drpykachu/Sonar-Watch/Hardware/Complete v3.0/Complete v3.0 3D models/SLDPRT/V3.0.SLDASM

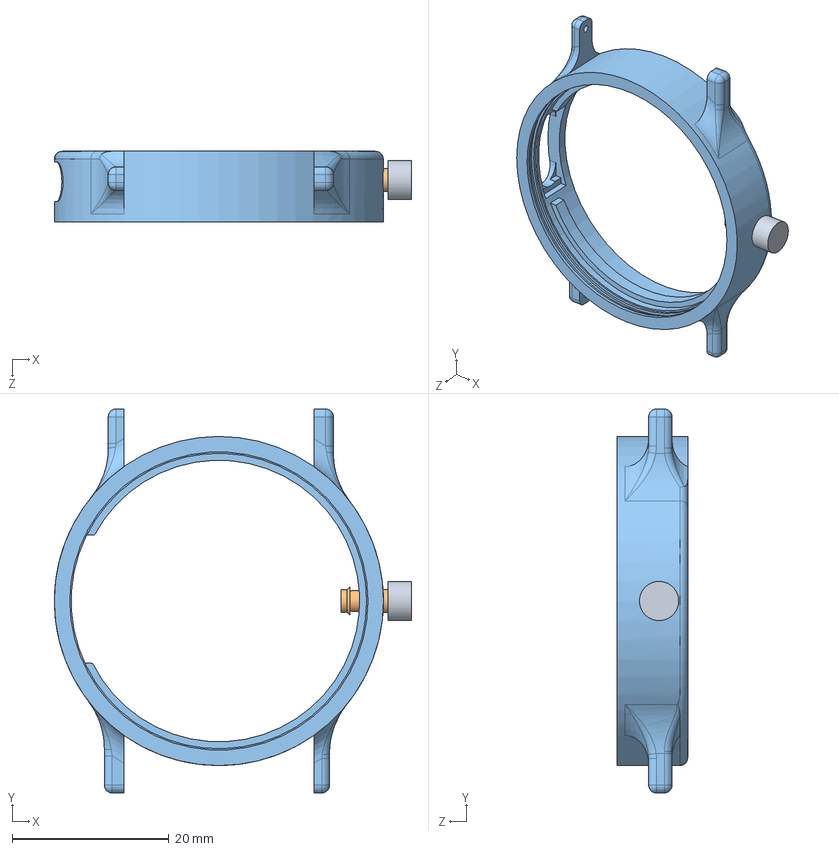
[picture p8: CAD file, 2025-09-28]
Hardware/Complete v3.0/Complete v3.0 3D models/SLDPRT/V3.0.SLDASM
45.6 x 49.0 x 9.00 mm
Body_NoNut
PushPin_inner
PushPin_cap
