drpykachu/Sonar-Watch/Parts/RMCF0603FT300K/RMCF0603FT300K.step

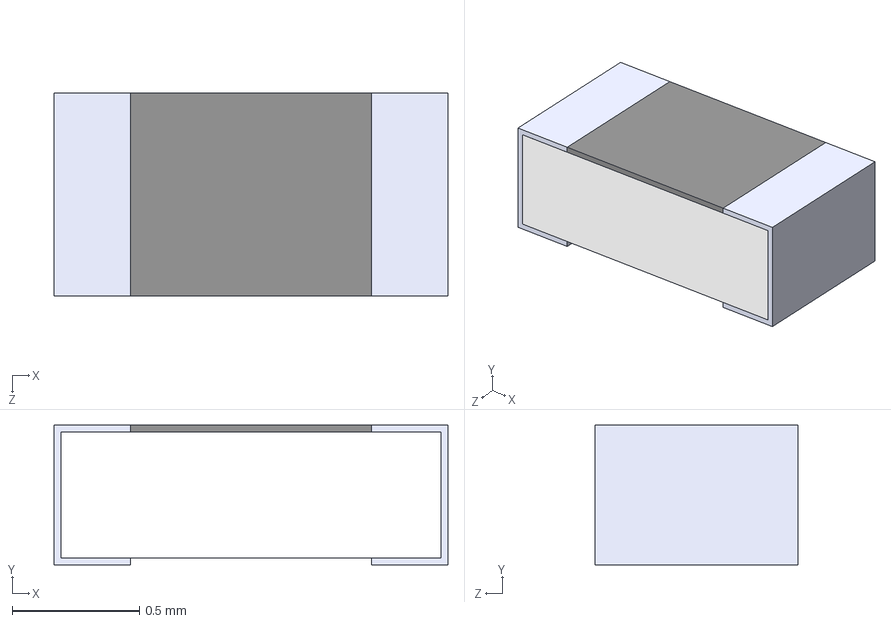
[picture p22: CAD file, 2025-05-27]
Parts/RMCF0603FT300K/RMCF0603FT300K.step
1.55 x 0.55 x 0.8 mm
