drpykachu/Sonar-Watch/Parts/RN73H1JTTD5052F50/RN73H1JTTD5052F50.step

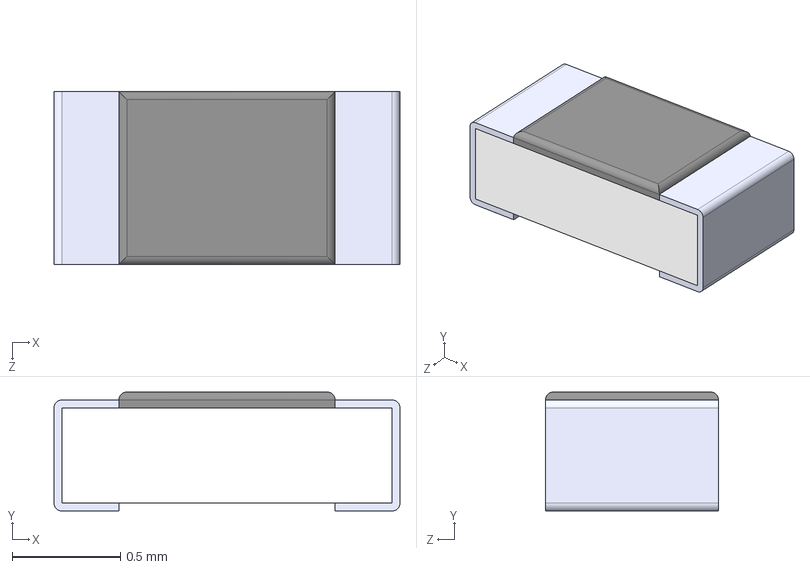
[picture p23: CAD file, 2025-05-20]
Parts/RN73H1JTTD5052F50/RN73H1JTTD5052F50.step
1.60 x 0.55 x 0.8 mm
