drpykachu/Sonar-Watch/Parts/TPS7A0230PDBVR/TPS7A0230PDBVR.stp

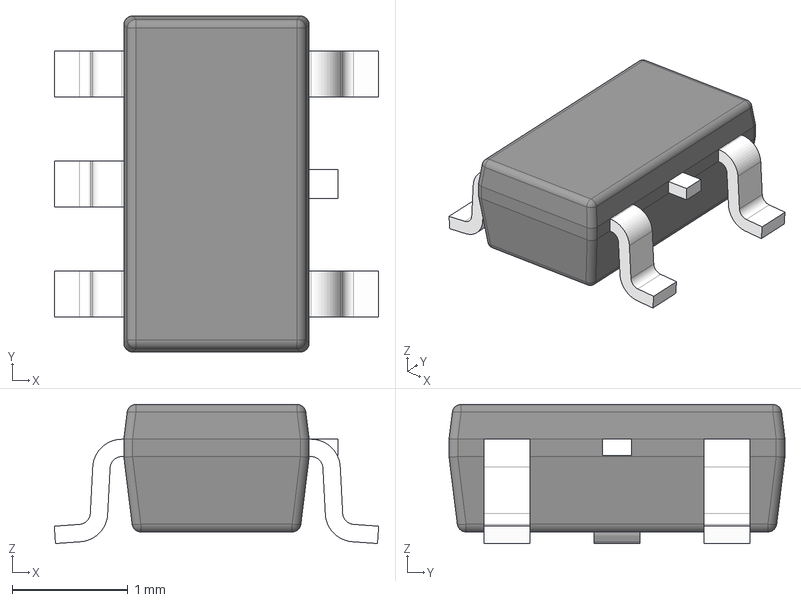
[picture p24: CAD file, 2025-05-20]
Parts/TPS7A0230PDBVR/TPS7A0230PDBVR.stp
2.80 x 2.90 x 1.20 mm
BODY-SOT
LEAD-SOT x 5
LEAD-DUMMY
