drpykachu/Sonar-Watch/Hardware/Charger v1.0/Case_All.SLDPRT

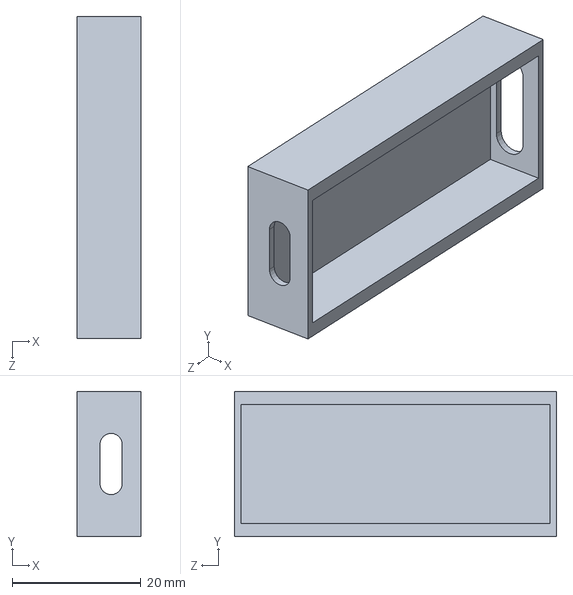
[picture p25: CAD file, 2025-08-06]
Hardware/Charger v1.0/Case_All.SLDPRT
10.0 x 22.5 x 50.0 mm
