drpykachu/Sonar-Watch/Hardware/Complete v3.0/Complete v3.0 3D models/SLDPRT/Body_NoNut.SLDPRT

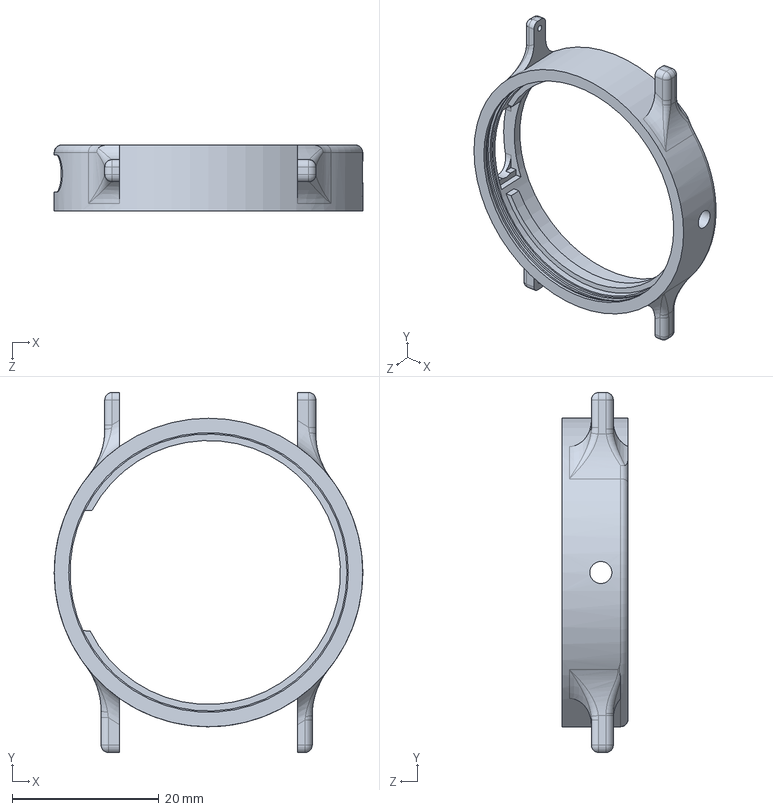
[picture p26: CAD file, 2025-09-28]
Hardware/Complete v3.0/Complete v3.0 3D models/SLDPRT/Body_NoNut.SLDPRT
42.0 x 49.0 x 9.00 mm
