drpykachu/Sonar-Watch/Hardware/Complete v3.0/Complete v3.0 3D models/STEP/button_board.step

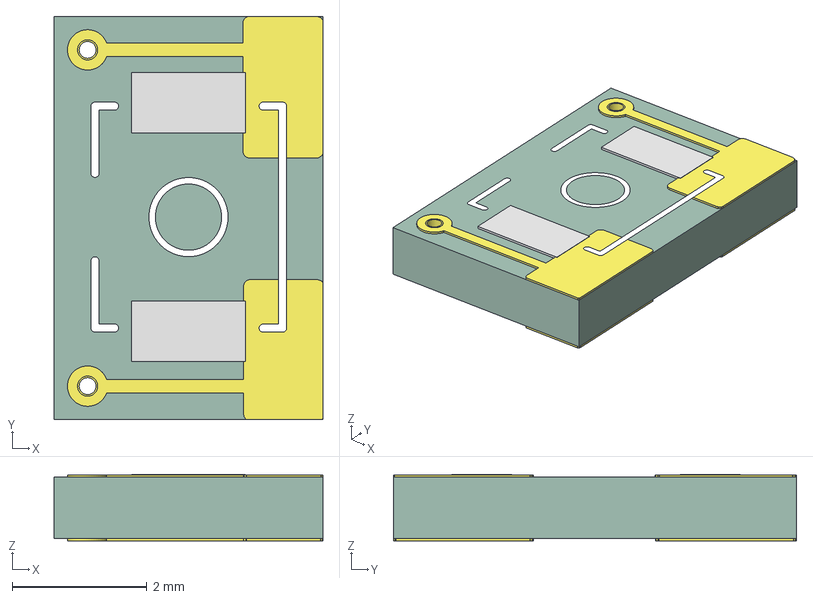
[picture p27: CAD file, 2025-08-06]
Hardware/Complete v3.0/Complete v3.0 3D models/STEP/button_board.step
4.00 x 6.00 x 1.02 mm
Button_Breakout_copper
Button_Breakout_pad
Button_Breakout_via
Button_Breakout_silkscreen
Button_Breakout_PCB
