drpykachu/Sonar-Watch/Parts/BAT-HLD-003-SMT/BAT-HLD-003-SMT.step

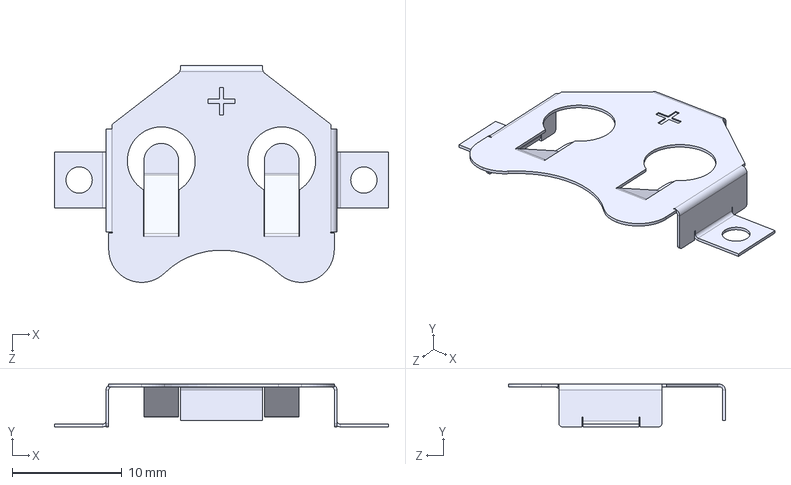
[picture p28: CAD file, 2025-05-14]
Parts/BAT-HLD-003-SMT/BAT-HLD-003-SMT.step
30.5 x 3.90 x 19.8 mm
