drpykachu/Sonar-Watch/Parts/Glass/Case.SLDPRT

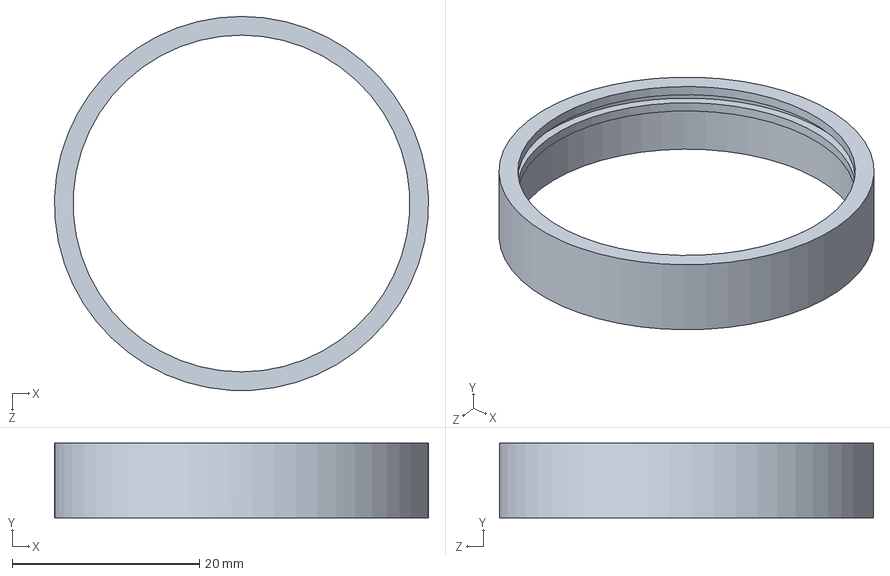
[picture p29: CAD file, 2025-05-27]
Parts/Glass/Case.SLDPRT
40.0 x 8.00 x 40.0 mm
