drpykachu/Sonar-Watch/Hardware/Complete v3.0/Complete v3.0 3D models/SLDPRT/PushPin_cap.SLDPRT

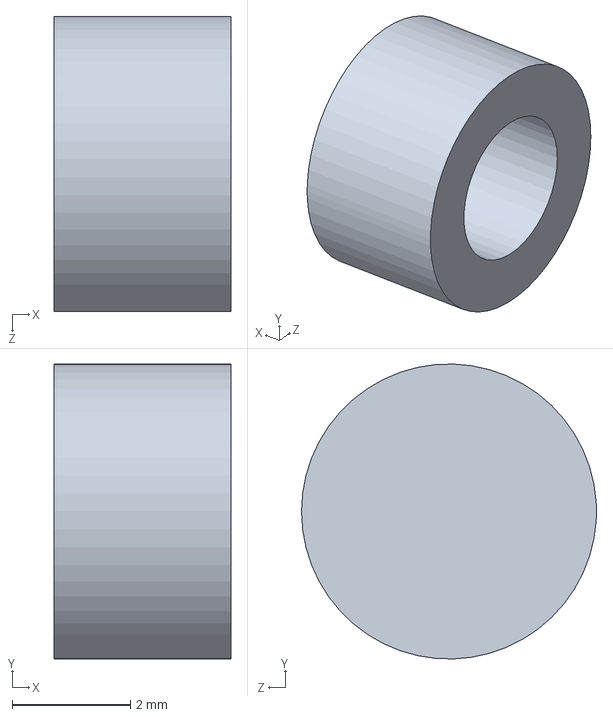
[picture p30: CAD file, 2025-09-28]
Hardware/Complete v3.0/Complete v3.0 3D models/SLDPRT/PushPin_cap.SLDPRT
3.00 x 5.00 x 5.00 mm
