drpykachu/Sonar-Watch/Hardware/Complete v3.0/Complete v3.0 3D models/STEP/POGO_board.step

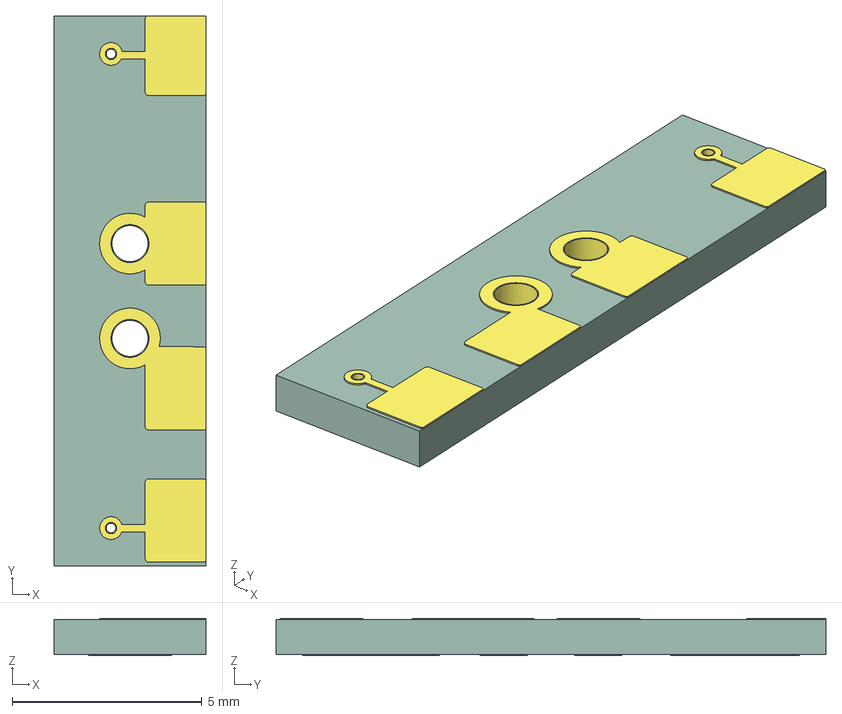
[picture p31: CAD file, 2025-06-30]
Hardware/Complete v3.0/Complete v3.0 3D models/STEP/POGO_board.step
4.00 x 14.5 x 0.98 mm
Pogo_Breakout_copper
Pogo_Breakout_via
Pogo_Breakout_PCB
