drpykachu/Sonar-Watch/Hardware/Complete v3.0/Complete v3.0 3D models/To Print/PushPin_inner.STL

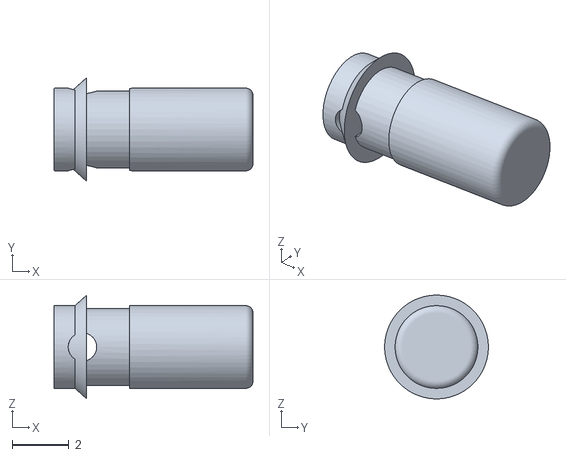
[picture p32: CAD file, 2025-09-28]
Hardware/Complete v3.0/Complete v3.0 3D models/To Print/PushPin_inner.STL
7.00 x 3.65 x 3.65
