drpykachu/Sonar-Watch/Parts/Glass/Glass_38mm_1mm.SLDPRT

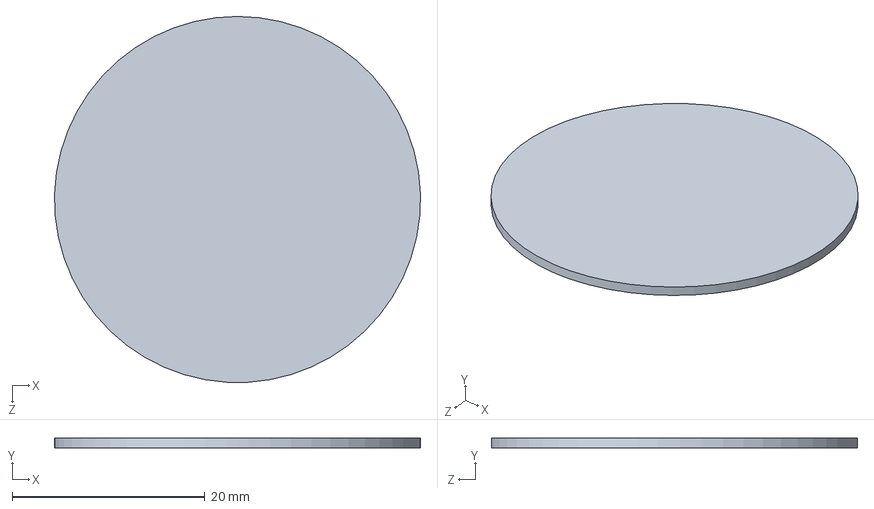
[picture p33: CAD file, 2025-05-27]
Parts/Glass/Glass_38mm_1mm.SLDPRT
38.0 x 1.00 x 38.0 mm
