drpykachu/Sonar-Watch/Parts/Pogo Pin Connector/Male.SLDPRT

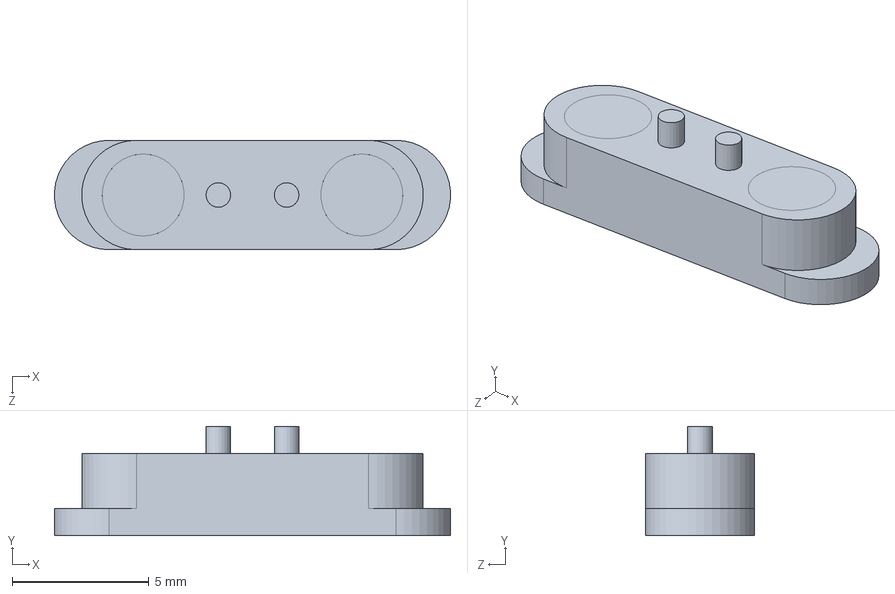
[picture p34: CAD file, 2025-05-14]
Parts/Pogo Pin Connector/Male.SLDPRT
14.5 x 4.00 x 4.00 mm
