drpykachu/Sonar-Watch/Hardware/Complete v3.0/Complete v3.0 3D models/SLDPRT/Solder Jig.SLDPRT

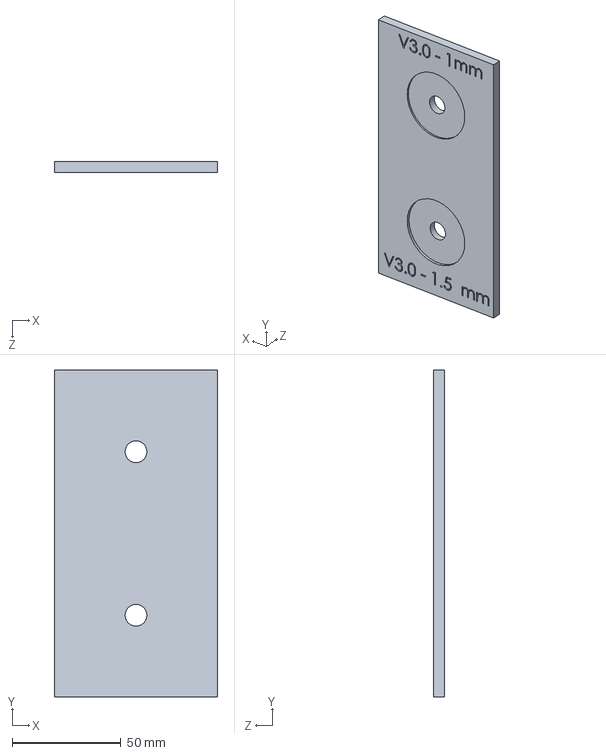
[picture p35: CAD file, 2025-09-28]
Hardware/Complete v3.0/Complete v3.0 3D models/SLDPRT/Solder Jig.SLDPRT
75.0 x 150.0 x 5.00 mm
