drpykachu/Sonar-Watch/Hardware/Complete v3.0/Complete v3.0 3D models/To Print/PushPin.STL

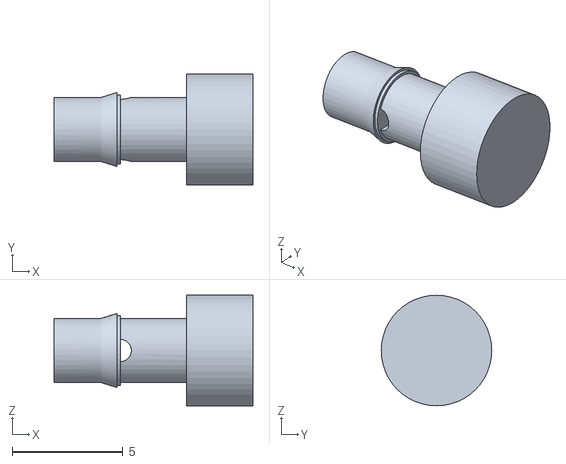
[picture p36: CAD file, 2025-09-28]
Hardware/Complete v3.0/Complete v3.0 3D models/To Print/PushPin.STL
9.00 x 5.00 x 5.00
