drpykachu/Sonar-Watch/Hardware/Complete v3.0/Complete v3.0 3D models/SLDPRT/Back.SLDPRT

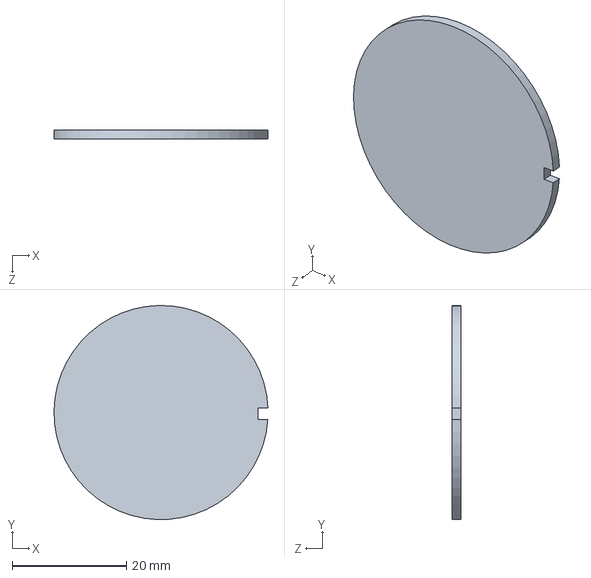
[picture p38: CAD file, 2025-09-28]
Hardware/Complete v3.0/Complete v3.0 3D models/SLDPRT/Back.SLDPRT
37.4 x 37.4 x 1.50 mm
