drpykachu/Sonar-Watch/Hardware/Complete v3.0/Complete v3.0 3D models/To Print/support.STL

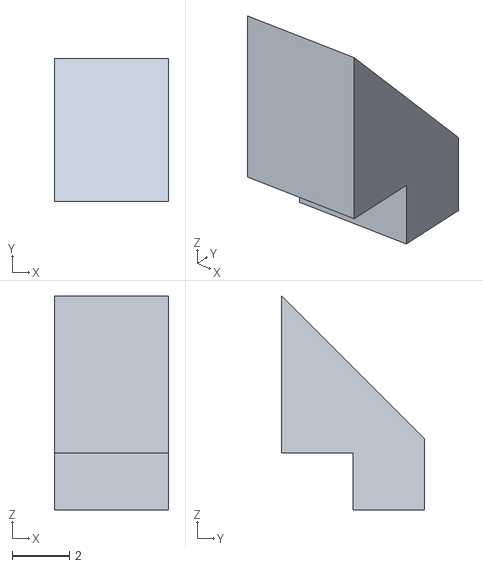
[picture p39: CAD file, 2025-08-06]
Hardware/Complete v3.0/Complete v3.0 3D models/To Print/support.STL
4.00 x 5.00 x 7.50
