drpykachu/Sonar-Watch/Hardware/Complete v3.0/Complete v3.0 3D models/SLDPRT/Body.SLDPRT

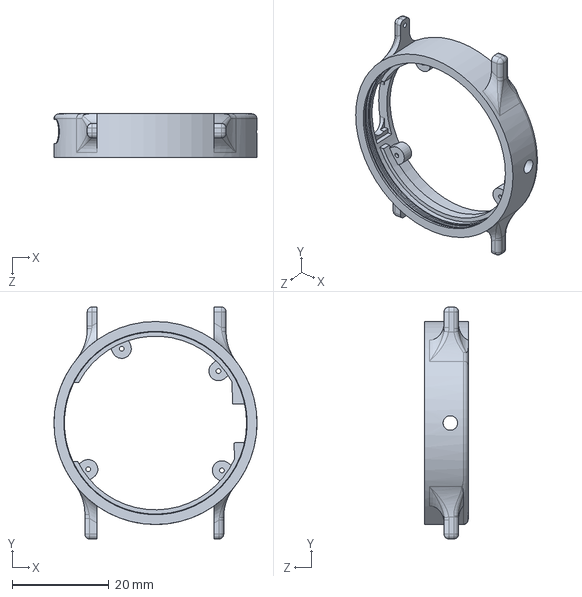
[picture p40: CAD file, 2025-09-28]
Hardware/Complete v3.0/Complete v3.0 3D models/SLDPRT/Body.SLDPRT
42.0 x 48.0 x 9.00 mm
