drpykachu/Sonar-Watch/Hardware/Complete v3.0/Complete v3.0 3D models/SLDPRT/Glass_38mm_1-2mm.SLDPRT

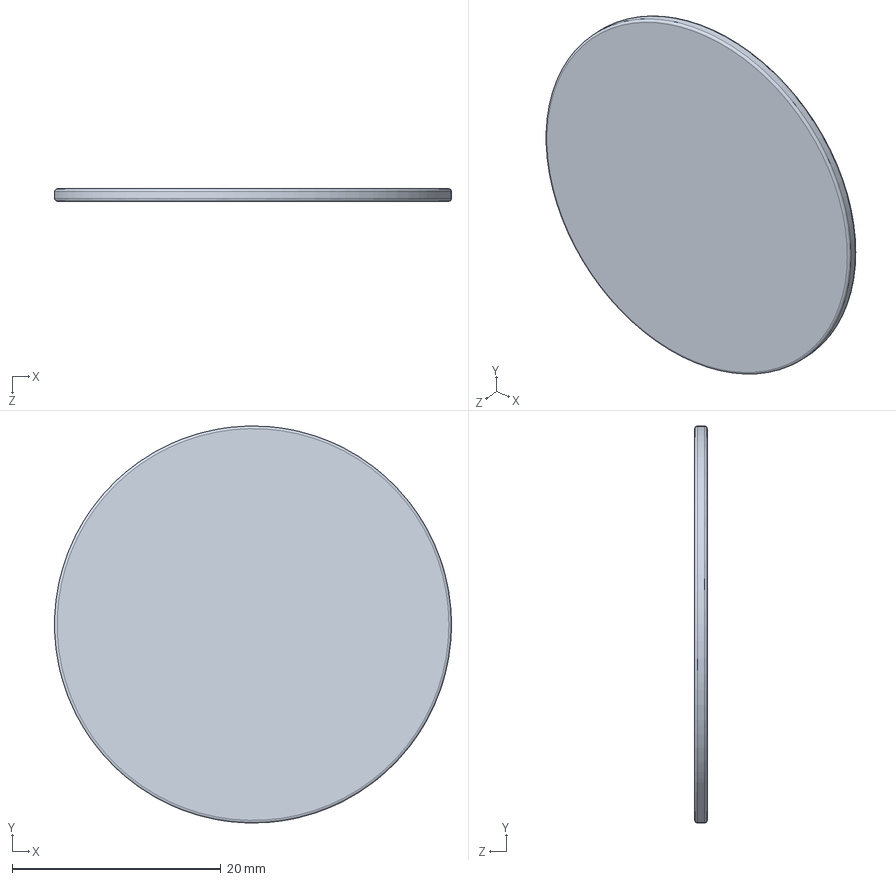
[picture p41: CAD file, 2025-08-06]
Hardware/Complete v3.0/Complete v3.0 3D models/SLDPRT/Glass_38mm_1-2mm.SLDPRT
38.0 x 38.0 x 1.20 mm
