drpykachu/Sonar-Watch/Software/Arduino/Main_PWRDWN_v4_0_0_Nate/WatchData.h

// WatchData.h

#ifndef WatchData_H
#define WatchData_H

extern int NaN;

//////////////////////////////////////////////////////////////// PHYSICAL PIN LOCATIONS

//          / Nets =   A, B, C, D, E, F, G,  H,  I,  J,  K,  L,  M,  N,  O,  P
const int pins[16] = { 4, 5, 6, 7, 8, 9, 10, 11, 12, 13, 24, 15, 16, 17, 18, 19 };
const int LED_count = 201;

//////////////////////////////////////////////////////////////// MACROS
#define NUMELEMENTS(x) (sizeof(x) / sizeof(x[0]))

//////////////////////////////////////////////////////////////// LED POSITION ARRAYS
// Low position LED array
const int HIGH_POS[] = {
  0, 4, 4, 6, 6, 8, 8, 10, 10, 1,  4, 0, 6, 4, 8, 6, 10, 8, 12, 10,  2, 4, 1, 6, 0, 8, 4, 10, 6, 12,  8, 13, 10, 3, 4, 2, 6, 1, 8, 0,
  10, 4, 12, 6, 13, 8, 14, 10, 4, 3,  6, 2, 8, 1, 10, 0, 12, 4, 13, 6,  14, 8, 15, 5, 6, 3, 8, 2, 10, 1,  12, 0, 13, 4, 14, 6, 15, 8, 6, 5,
  8, 3, 10, 2, 12, 1, 13, 0, 14, 4,  15, 6, 11, 7, 8, 5, 10, 3, 12, 2,  13, 1, 14, 0, 15, 4, 11, 6, 8, 7,  10, 5, 12, 3, 13, 2, 14, 1, 15, 0,
  11, 4, 9, 9, 10, 7, 12, 5, 13, 3,  14, 2, 15, 1, 11, 0, 9, 4, 10, 9,  12, 7, 13, 5, 14, 3, 15, 2, 11, 1,  9, 0, 7, 11, 12, 9, 13, 7, 14, 5,
  15, 3, 11, 2, 9, 1, 7, 0, 11, 13,  9, 14, 7, 15, 5, 11, 3, 9, 2, 7,  1, 11, 14, 9, 15, 7, 11, 5, 9, 3,  7, 2, 11, 15, 9, 11, 7, 9, 5, 7, 3};

// High position LED array
const int LOW_POS[] = {
  4, 0, 6, 4, 8, 6, 10, 8, 12, 4,  1, 6, 0, 8, 4, 10, 6, 12, 8, 13,  4, 2, 6, 1, 8, 0, 10, 4, 12, 6,  13, 8, 14, 4, 3, 6, 2, 8, 1, 10,
  0, 12, 4, 13, 6, 14, 8, 15, 5, 6,  3, 8, 2, 10, 1, 12, 0, 13, 4, 14,  6, 15, 8, 6, 5, 8, 3, 10, 2, 12,  1, 13, 0, 14, 4, 15, 6, 11, 7, 8,
  5, 10, 3, 12, 2, 13, 1, 14, 0, 15,  4, 11, 6, 8, 7, 10, 5, 12, 3, 13,  2, 14, 1, 15, 0, 11, 4, 9, 9, 10,  7, 12, 5, 13, 3, 14, 2, 15, 1, 11,
  0, 9, 4, 10, 9, 12, 7, 13, 5, 14,  3, 15, 2, 11, 1, 9, 0, 7, 11, 12,  9, 13, 7, 14, 5, 15, 3, 11, 2, 9,  1, 7, 0, 12, 11, 13, 9, 14, 7, 15,
  5, 11, 3, 9, 2, 7, 1, 5, 13, 11,  14, 9, 15, 7, 11, 5, 9, 3, 7, 2,  5, 14, 11, 15, 9, 11, 7, 9, 5, 7,  3, 5, 15, 11, 11, 9, 9, 7, 7, 5, 5};


//////////////////////////////////////////////////////////////// DIAGONAL PULSE ARRAY/STRUCTURE

struct RINGS {
  int *pins;
  uint16_t numElements;
};


const int ring0[] = { 101 };
const int ring1[] = { 86, 100, 102, 116 };
const int ring2[] = { 71, 85, 87, 99, 103, 115, 117, 131 };
const int ring3[] = { 56, 70, 72, 84, 88, 98, 104, 114, 118, 130, 132, 146 };
const int ring4[] = { 41, 55, 57, 69, 73, 83, 89, 97, 105, 113, 119, 129, 133, 145, 147, 161 };
const int ring5[] = { 27, 40, 42, 54, 58, 68, 74, 82, 90, 96, 106, 112, 120, 128, 134, 144, 148, 160, 162, 175 };
const int ring6[] = { 15, 26, 28, 39, 43, 53, 59, 67, 75, 81, 91, 95, 107, 111, 121, 127, 135, 143, 149, 159, 163, 174, 176, 187 };
const int ring7[] = { 5, 14, 16, 25, 29, 38, 44, 52, 60, 66, 76, 80, 92, 94, 108, 110, 122, 126, 136, 142, 150, 158, 164, 173, 177, 186, 188, 197 };
const int ring8[] = { 4, 6, 13, 17, 24, 30, 37, 45, 51, 61, 65, 77, 79, 93, 109, 123, 125, 137, 141, 151, 157, 165, 172, 178, 185, 189, 196, 198 };
const int ring9[] = { 3, 7, 12, 18, 23, 31, 36, 46, 50, 62, 64, 78, 124, 138, 140, 152, 156, 166, 171, 179, 184, 190, 195, 199 };
const int ring10[] = { 2, 8, 11, 19, 22, 32, 35, 47, 49, 63, 139, 153, 155, 167, 170, 180, 183, 191, 194, 200 };
const int ring11[] = { 1, 9, 10, 20, 21, 33, 34, 48, 154, 168, 169, 181, 182, 192, 193, 201 };

RINGS ringMatrix[] =
{  {ring0, NUMELEMENTS(ring0)},  {ring1, NUMELEMENTS(ring1)},  {ring2, NUMELEMENTS(ring2)},  {ring3, NUMELEMENTS(ring3)},
  {ring4, NUMELEMENTS(ring4)},  {ring5, NUMELEMENTS(ring5)},  {ring6, NUMELEMENTS(ring6)},  {ring7, NUMELEMENTS(ring7)},
  {ring8, NUMELEMENTS(ring8)},  {ring9, NUMELEMENTS(ring9)},  {ring10, NUMELEMENTS(ring10)},  {ring11, NUMELEMENTS(ring11)},};


/////////////////////////////////////// LARGE SEVEN SEGMENT ARRAY/STRUCTURE
const int large_seg0[] = {40,41,42,58,73,88,118,133,148,162,161,160,144,129,114,84,69,54,99,103};
const int large_seg1[] = {41,56,71,86,101,116,131,146,161};
const int large_seg2[] = {40,41,42,58,73,88,102,101,100,114,129,144,160,161,162};
const int large_seg3[] = {40,41,42,58,73,88,102,101,100,118,133,148,162,161,160};
const int large_seg4[] = {54,69,84,100,101,102,58,73,88,118,133,148,103};
const int large_seg5[] = {42,41,40,54,69,84,100,101,102,118,133,148,162,161,160};
const int large_seg6[] = {42,41,40,54,69,84,100,101,102,118,133,148,162,161,160,144,129,114};
const int large_seg7[] = {40,41,42,58,73,88,103,118,133,148};
const int large_seg8[] = {40,41,42,58,73,88,118,133,148,162,161,160,144,129,114,84,69,54,100,101,102};
const int large_seg9[] = {40,41,42,58,73,88,118,133,148,84,69,54,100,101,102};

RINGS large_seg7_matrix[] = 
{  {large_seg0, NUMELEMENTS(large_seg0)}, {large_seg1, NUMELEMENTS(large_seg1)}, {large_seg2, NUMELEMENTS(large_seg2)}, 
  {large_seg3, NUMELEMENTS(large_seg3)}, {large_seg4, NUMELEMENTS(large_seg4)}, {large_seg5, NUMELEMENTS(large_seg5)}, 
  {large_seg6, NUMELEMENTS(large_seg6)}, {large_seg7, NUMELEMENTS(large_seg7)}, {large_seg8, NUMELEMENTS(large_seg8)}, 
  {large_seg9, NUMELEMENTS(large_seg9)}};



/////////////////////////////////////// SMALL SEVEN SEGMENT ARRAY/STRUCTURE
const int small_seg0[] = {72,71,70,85,100,115,130,131,132,117,102,87};
const int small_seg1[] = {71,86,101,116,131};
const int small_seg2[] = {70,71,72,87,102,101,100,115,130,131,132};
const int small_seg3[] = {70,71,72,87,100,101,102,117,132,131,130};
const int small_seg4[] = {70,85,100,101,102,87,72,117,132};
const int small_seg5[] = {70,72,71,70,85,100,101,102,117,132,131,130};
const int small_seg6[] = {72,71,70,85,100,101,102,115,130,131,132,117};
const int small_seg7[] = {70,71,72,87,102,117,132};
const int small_seg8[] = {70,71,72,87,102,117,132,131,130,115,100,101,85};
const int small_seg9[] = {70,71,72,87,102,117,132,100,101,85};

RINGS small_seg7_matrix[] = 
{  {small_seg0, NUMELEMENTS(small_seg0)}, {small_seg1, NUMELEMENTS(small_seg1)}, {small_seg2, NUMELEMENTS(small_seg2)}, 
  {small_seg3, NUMELEMENTS(small_seg3)}, {small_seg4, NUMELEMENTS(small_seg4)}, {small_seg5, NUMELEMENTS(small_seg5)}, 
  {small_seg6, NUMELEMENTS(small_seg6)}, {small_seg7, NUMELEMENTS(small_seg7)}, {small_seg8, NUMELEMENTS(small_seg8)}, 
  {small_seg9, NUMELEMENTS(small_seg9)}};

/////////////////////////////////////// PING AND 4DIG ARRAY/STRUCTURE

const int PING[] = {64,65,66,79,81,94,95,96,109,124,68,83,98,113,128,70,85,100,115,130,86,102,73,88,103,118,133,76,77,90,105,120,136,137,123,108,107};
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
  { 0, 0, 0, 0, 0, 0, 0, 0, 0, 0, 0, 0, 0, 0, 0 },              // 11
  { NaN, 0, 0, 0, 0, 0, 0, 0, 0, 0, 0, 0, 0, 0, NaN },          // 12
  { NaN, NaN, 0, 0, 0, 0, 0, 0, 0, 0, 0, 0, 0, NaN, NaN },      // 13
  { NaN, NaN, NaN, 0, 0, 0, 0, 0, 0, 0, 0, 0, NaN, NaN, NaN }   // 14
};


#endif
